Resaj/solder-paste-dispenser/images/IMG_20190203_000344.jpg

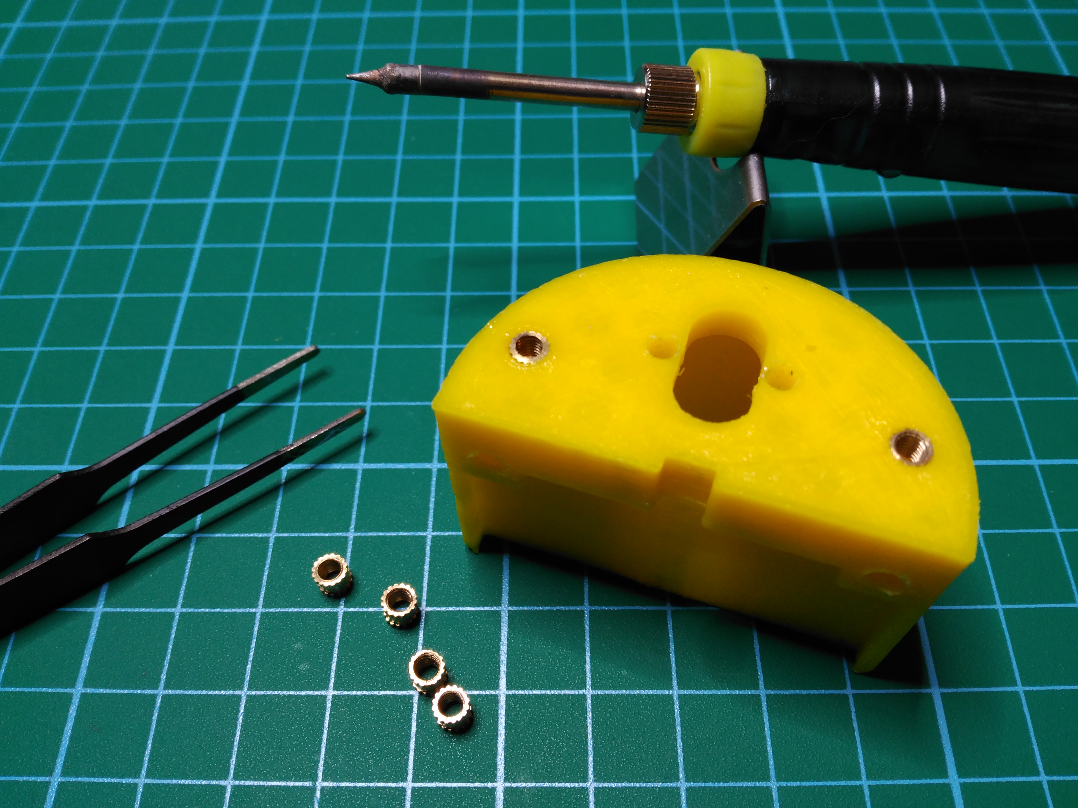
images/IMG_20190203_000344.jpg
