Resaj/solder-paste-dispenser/images/IMG_20190203_000905.jpg

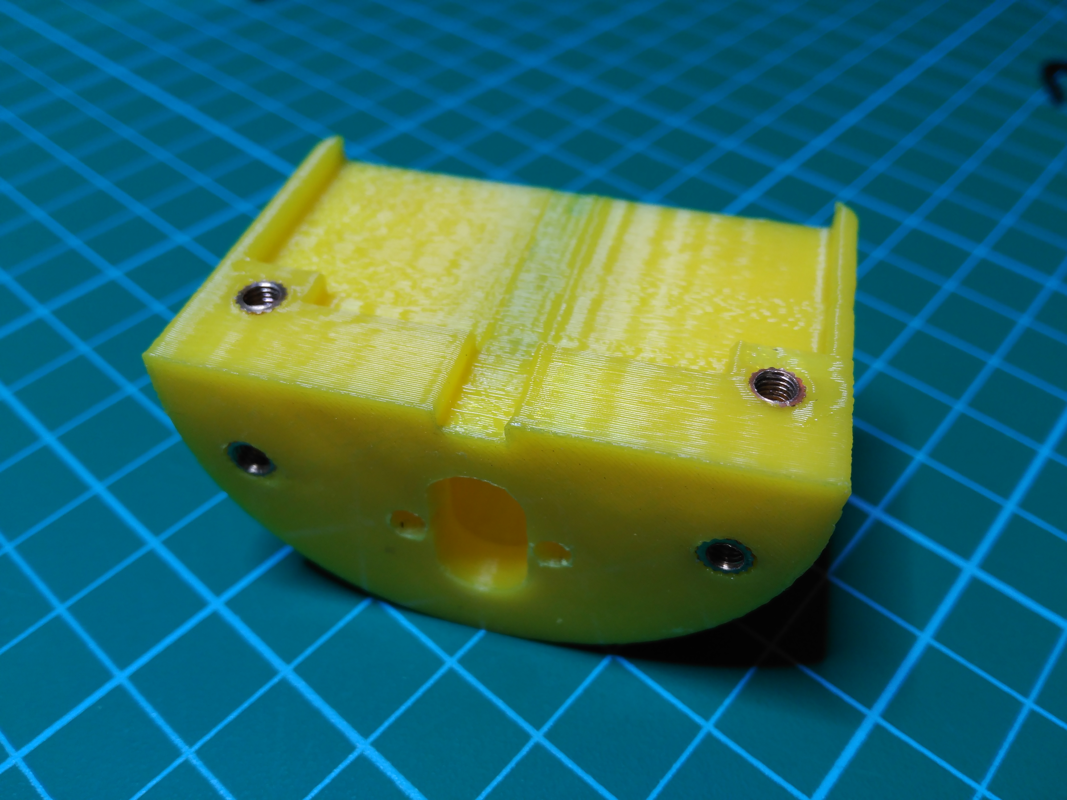
images/IMG_20190203_000905.jpg
