Resaj/solder-paste-dispenser/images/IMG_20190203_001242.jpg

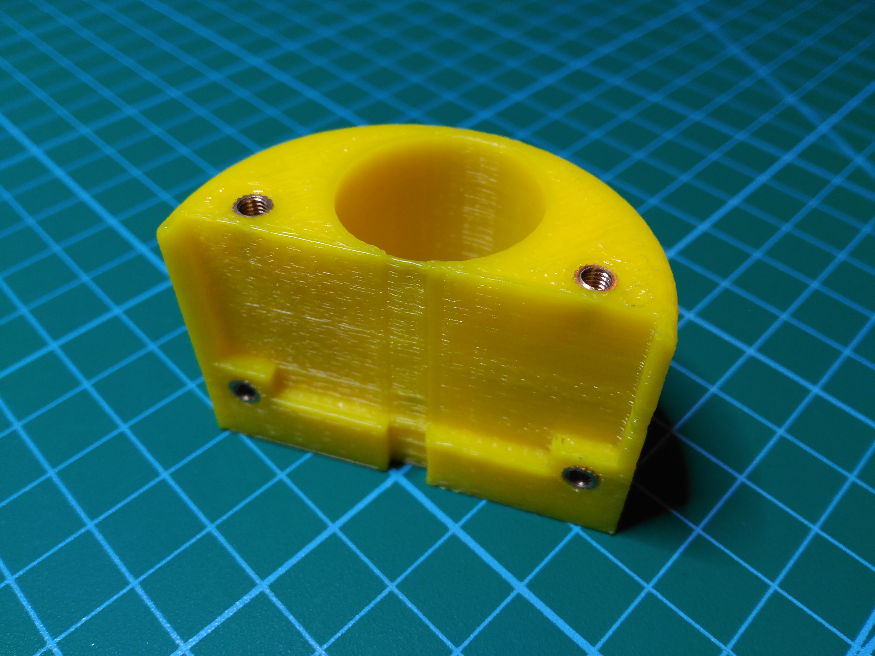
images/IMG_20190203_001242.jpg
