Resaj/solder-paste-dispenser/images/IMG_20190203_123748.jpg

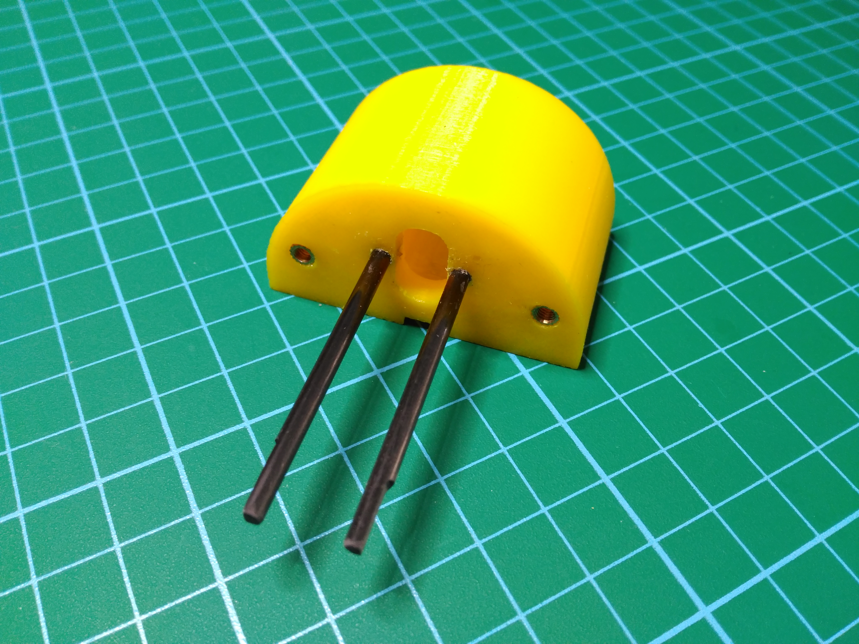
images/IMG_20190203_123748.jpg
