Resaj/solder-paste-dispenser/images/IMG_20190203_123901.jpg

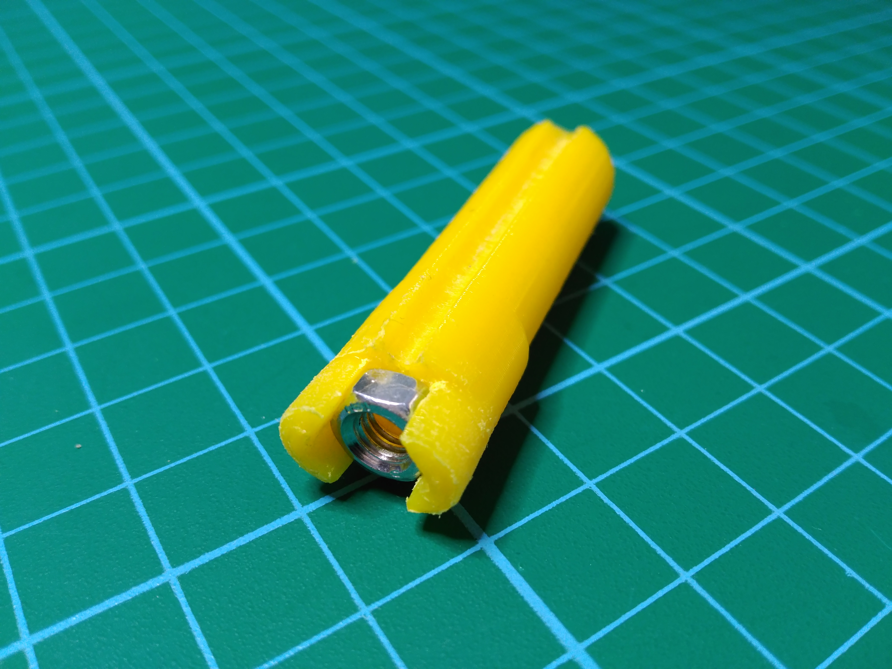
images/IMG_20190203_123901.jpg
