Resaj/solder-paste-dispenser/images/IMG_20190203_124237.jpg

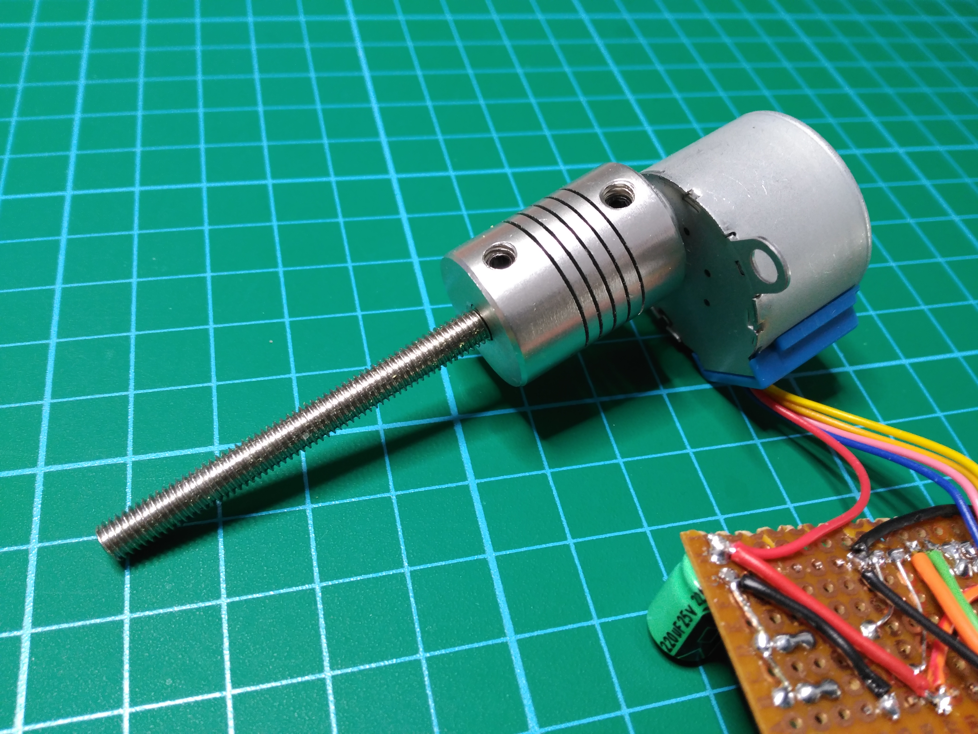
images/IMG_20190203_124237.jpg
