Resaj/solder-paste-dispenser/images/IMG_20190203_124618.jpg

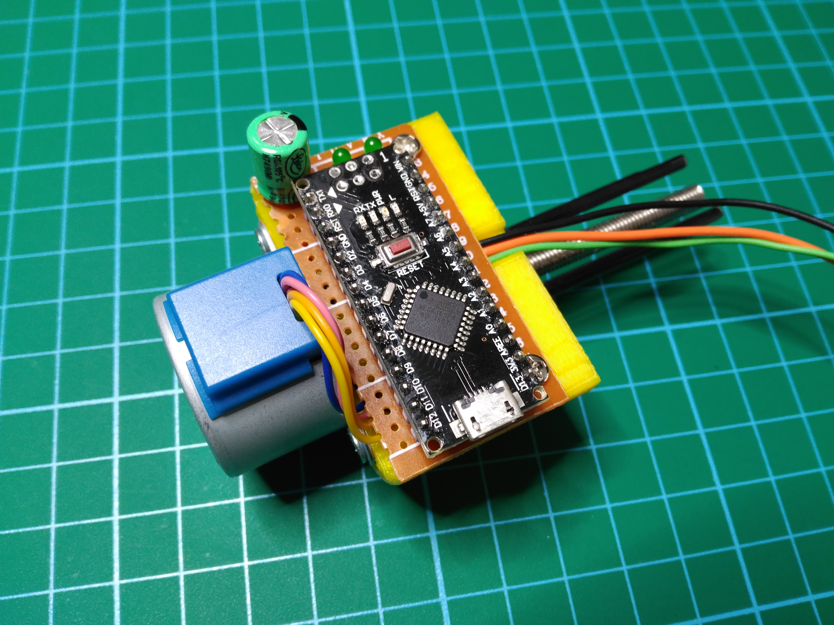
images/IMG_20190203_124618.jpg
