Resaj/solder-paste-dispenser/images/IMG_20190203_124844.jpg

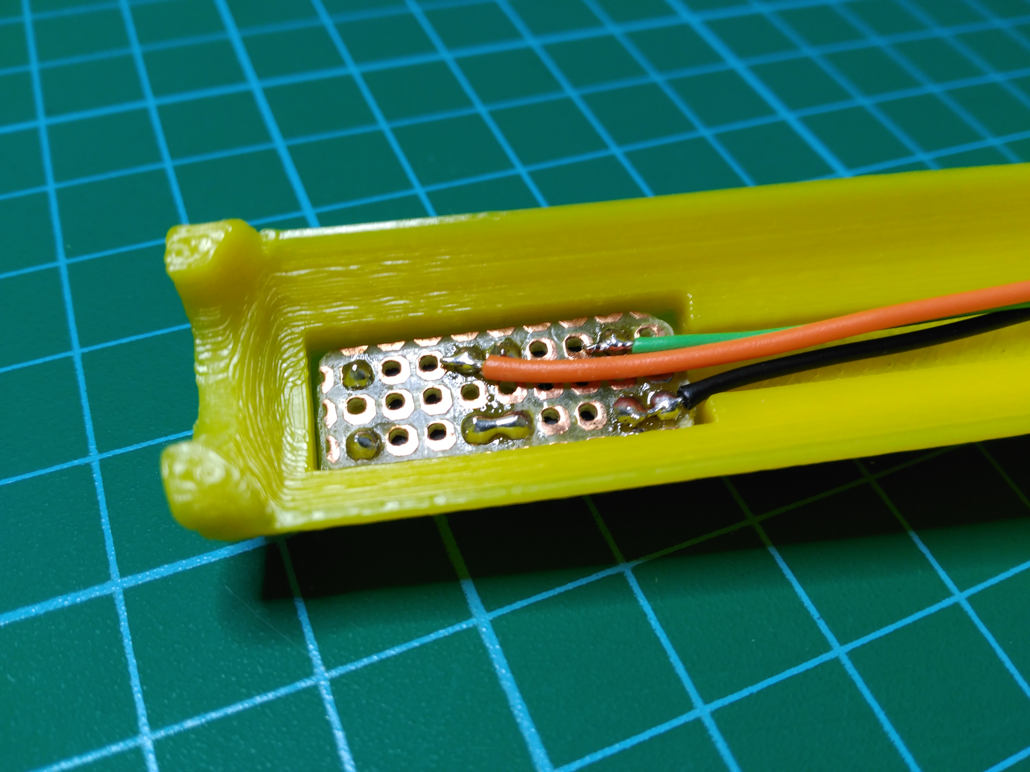
images/IMG_20190203_124844.jpg
