Resaj/solder-paste-dispenser/images/IMG_20190203_124907.jpg

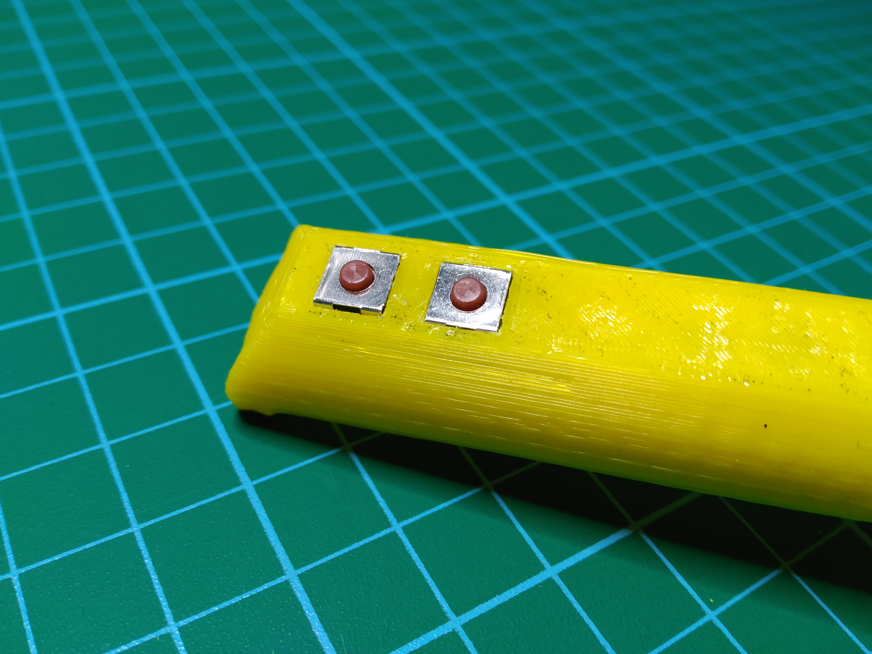
images/IMG_20190203_124907.jpg
