Resaj/solder-paste-dispenser/images/IMG_20190203_134759.jpg

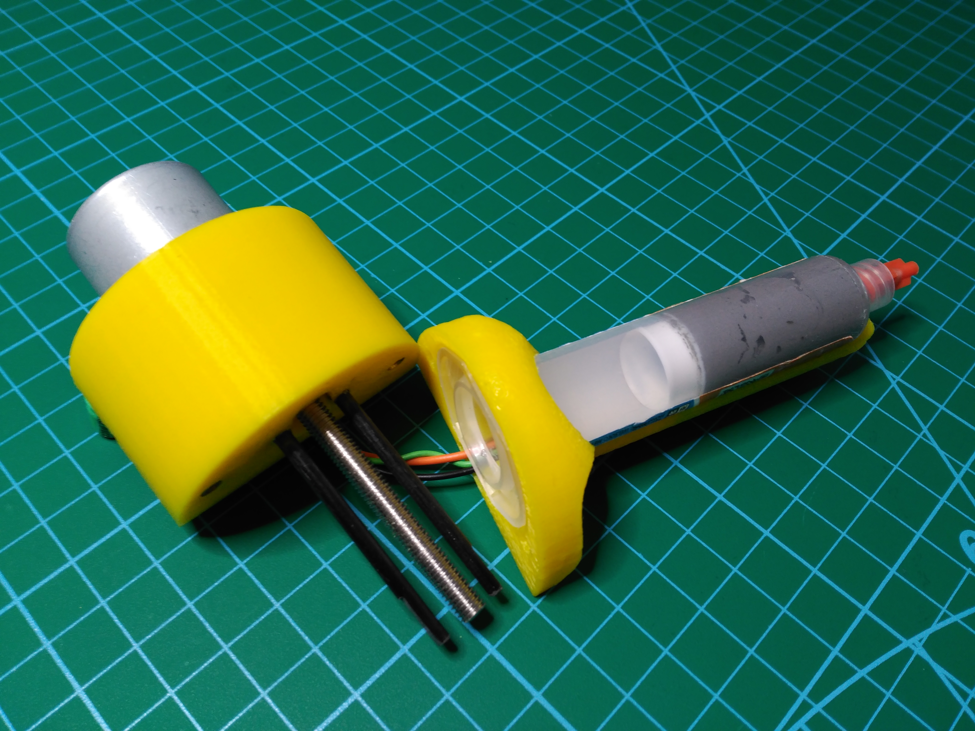
images/IMG_20190203_134759.jpg
