Resaj/solder-paste-dispenser/images/IMG_20190203_134817.jpg

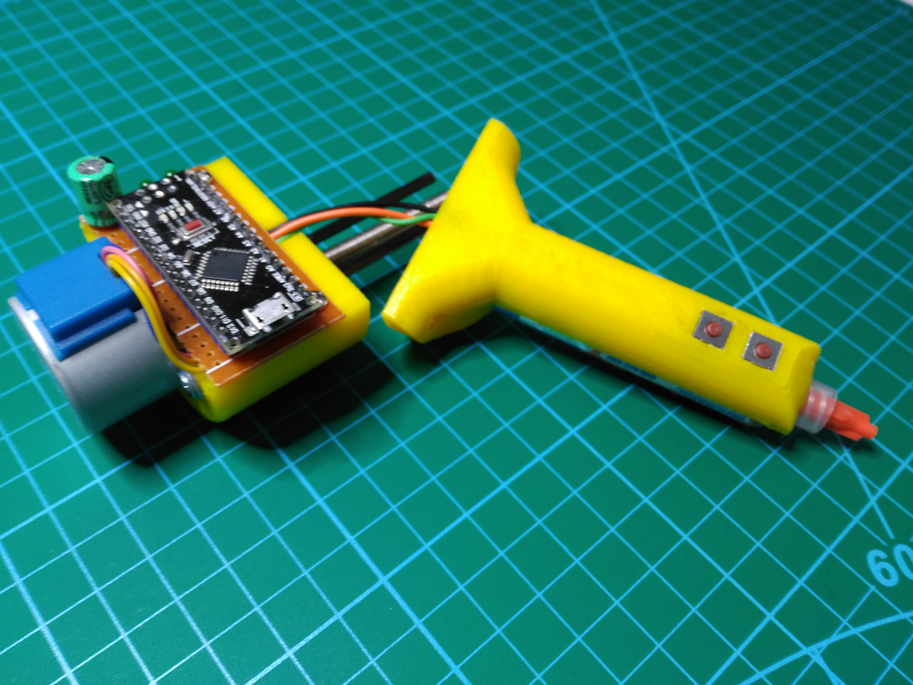
images/IMG_20190203_134817.jpg
