Resaj/solder-paste-dispenser/images/IMG_20190203_135938.jpg

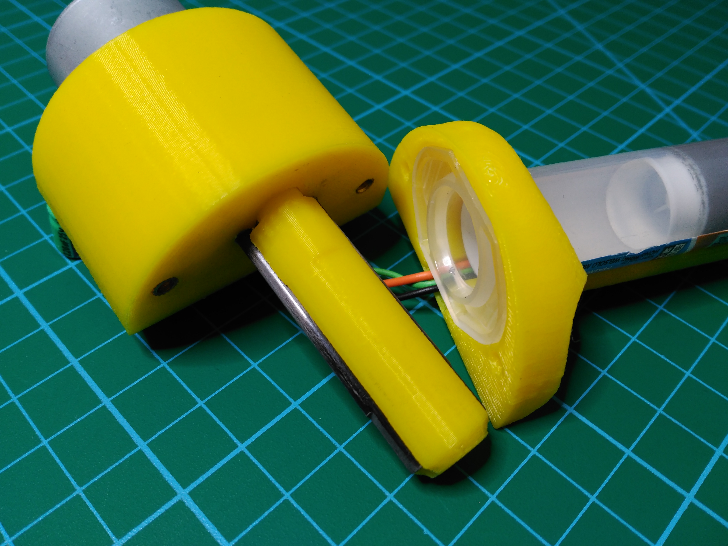
images/IMG_20190203_135938.jpg
