Resaj/solder-paste-dispenser/images/IMG_20190203_140006.jpg

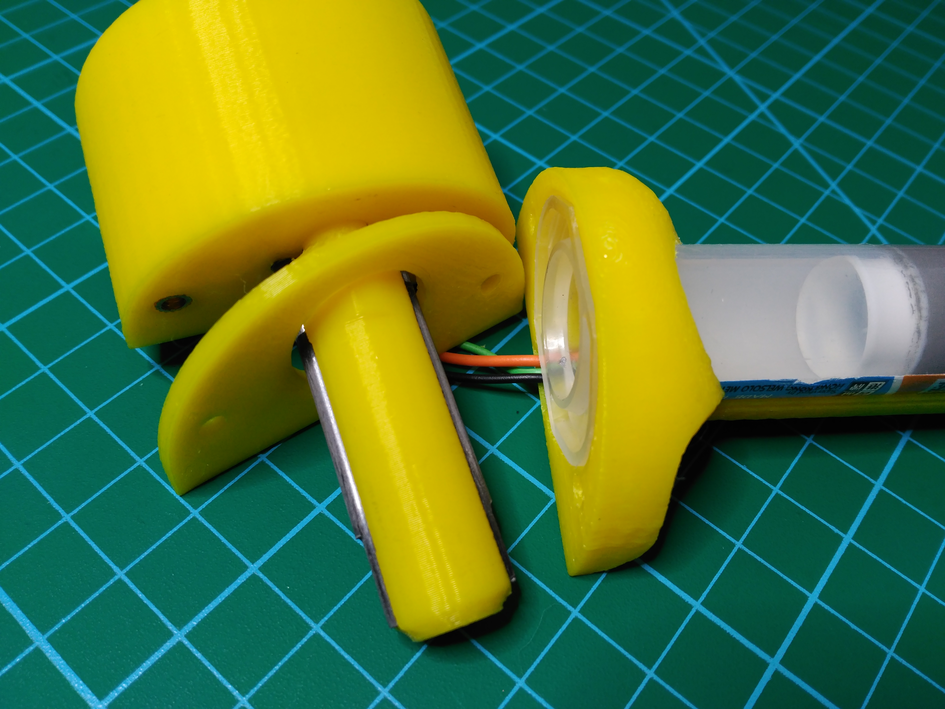
images/IMG_20190203_140006.jpg
