Resaj/solder-paste-dispenser/images/IMG_20190203_140219.jpg

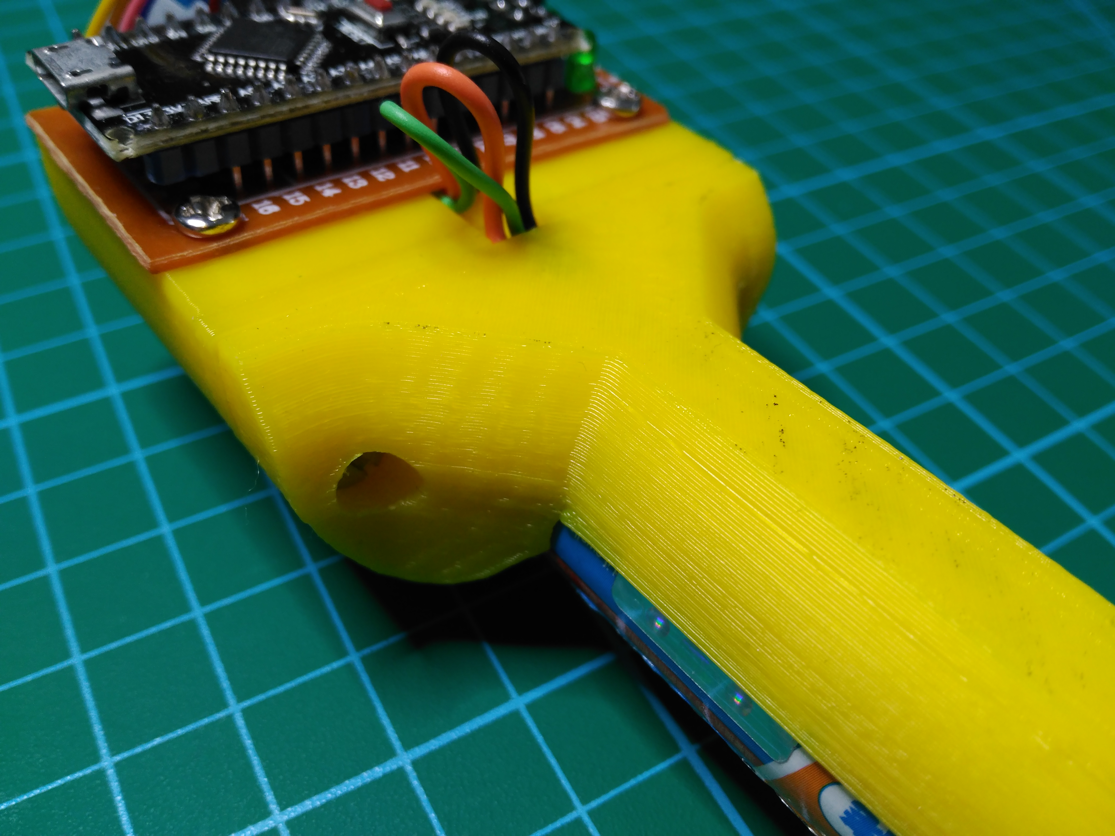
images/IMG_20190203_140219.jpg
